brainsmoke/aluball/scad/bracket_b_24x.scad

use <facet.scad>;
rotate([180,0,0])
ball_bracket(3,100);
