brainsmoke/aluball/scad/bracket_c_12x.scad

use <facet.scad>;
rotate([180,0,0])
ball_bracket(0,100);
